KKSSJJ1112/UNCZ_Slime_tracker/_OLDS/Measurement_Pic/1--00222.jpg

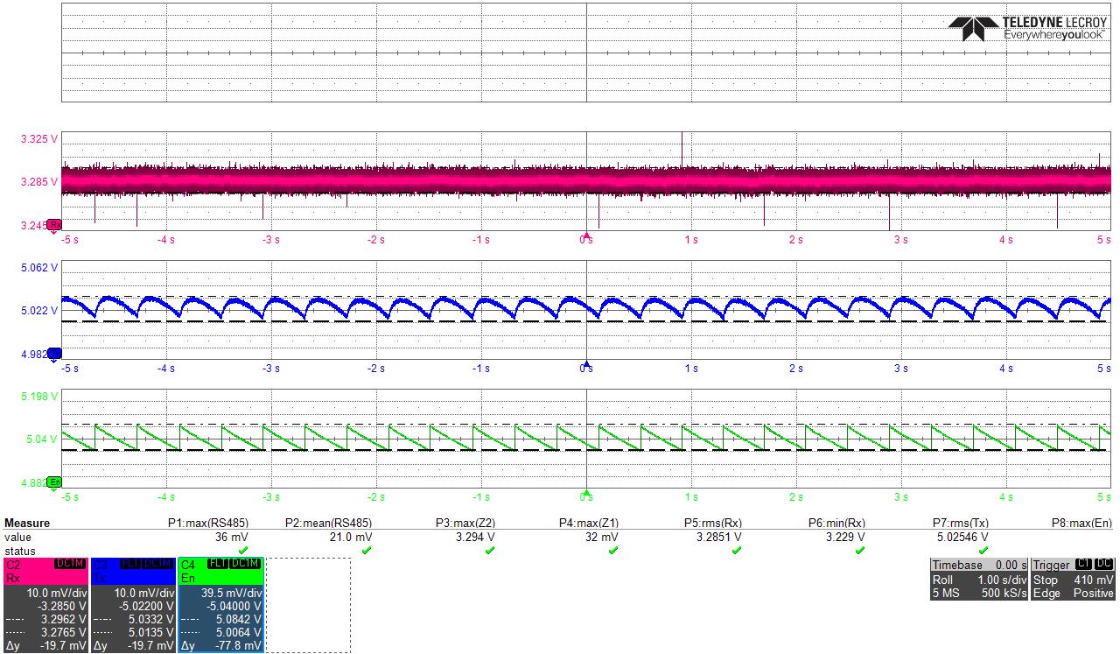
_OLDS/Measurement_Pic/1--00222.jpg
